Franzininho/Franzininho-WIFI-dev-edition/img/2.jpeg

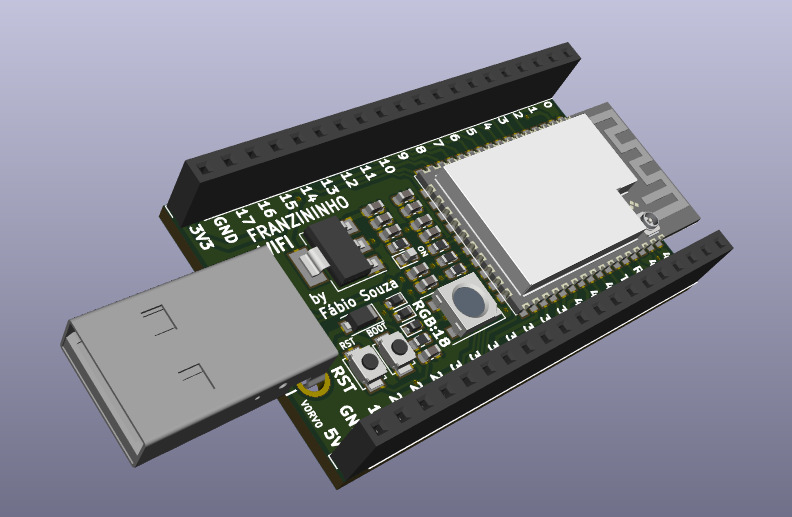
img/2.jpeg
