Franzininho/Franzininho-WIFI-dev-edition/img/Franzininho WIFI.jpg

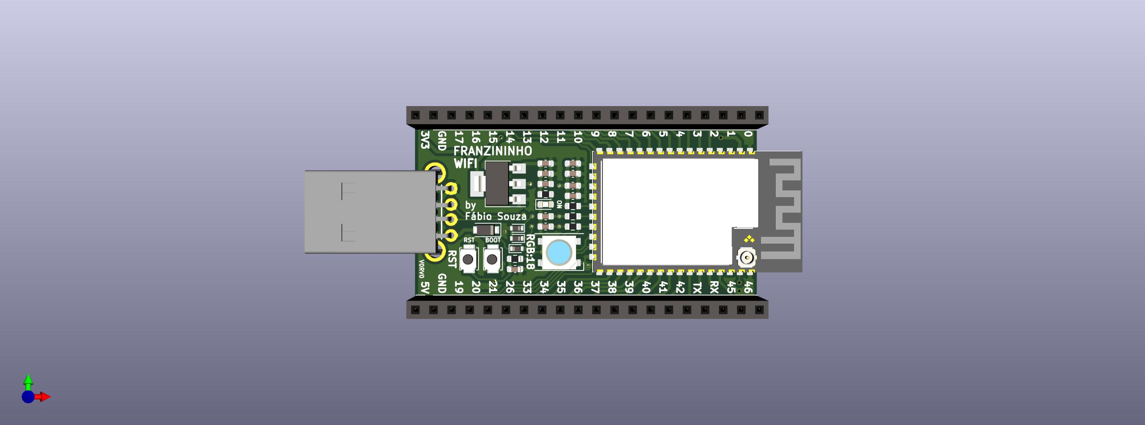
img/Franzininho WIFI.jpg
